gabrielebarola/Energy-Meter-progetto-PCTO/kicad/misura_corrente/top.pdf

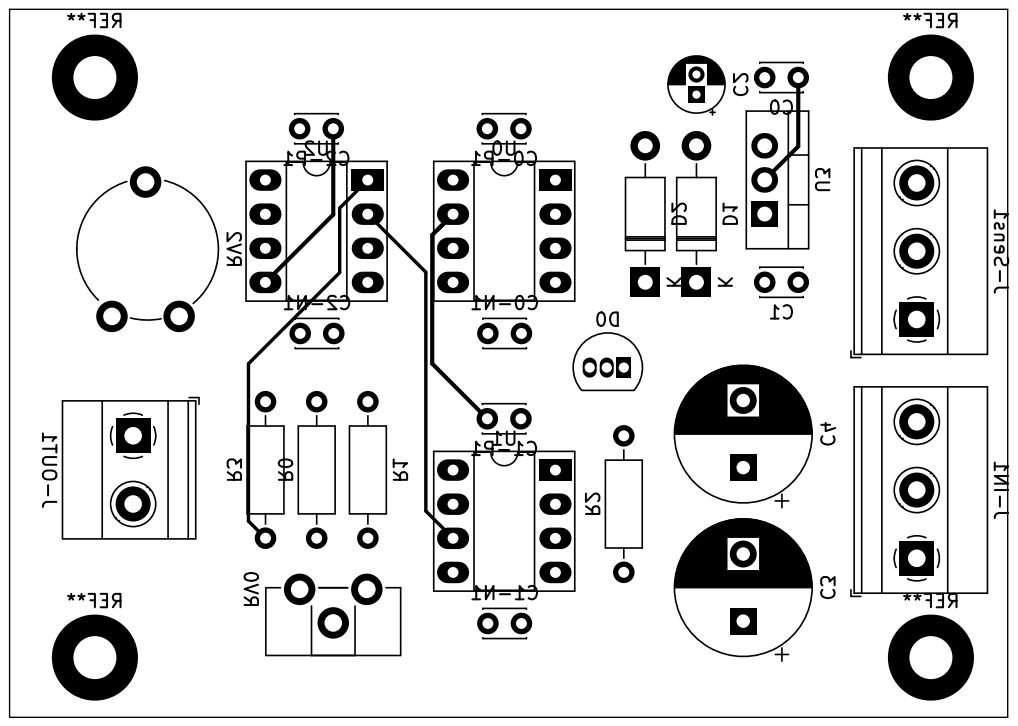
[picture p12: page 1]
