gabrielebarola/Energy-Meter-progetto-PCTO/kicad/misura_corrente/silk.pdf

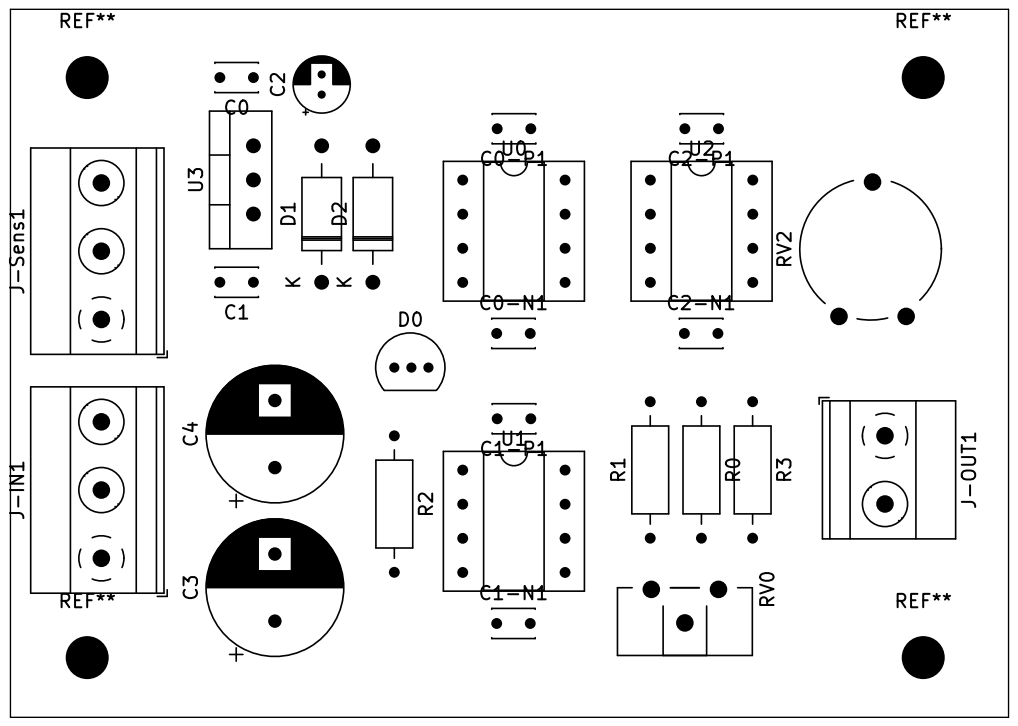
[picture p13: page 1]
