gabrielebarola/Energy-Meter-progetto-PCTO/firmware/esp32/boot.py

# This file is executed on every boot (including wake-boot from deepsleep)
# import esp
# esp.osdebug(None)
# import webrepl
# webrepl.start()

import ntptime


def wlan_connect(ssid="MYSSID", password="MYPASS"):
    import network

    wlan = network.WLAN(network.STA_IF)
    if not wlan.active() or not wlan.isconnected():
        wlan.active(True)
        print("connecting to:", ssid)
        wlan.connect(ssid, password)
        while not wlan.isconnected():
            pass
    print("network config:", wlan.ifconfig())


wlan_connect("gab", "******")
while True:
    try:
        ntptime.settime()
        break
    except OSError:
        continue
